Freimor/Protogen_Helmet_1/3d_models/helmet_rim(PETG).3mf

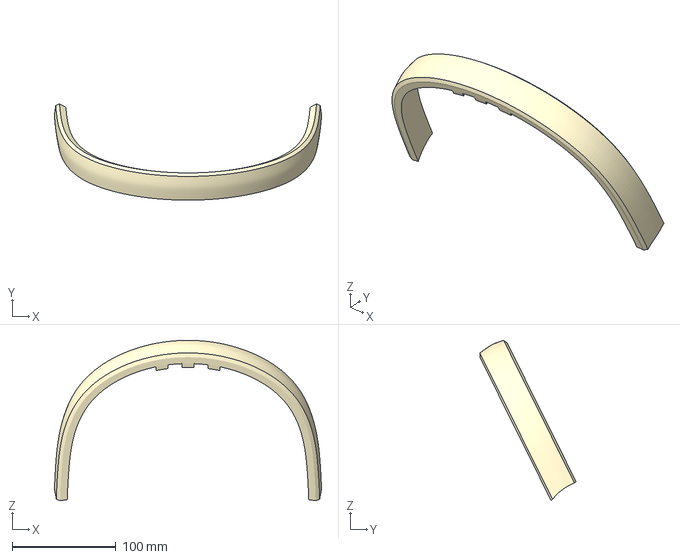
[picture p19: CAD file, 2022-10-17]
3d_models/helmet_rim(PETG).3mf
257.7 x 93.0 x 154.7 mm
